MakersAsylumIndia/IS2026_SU_Team02_NeuroPixel/Photos_Videos/Images/PHOTO-2026-05-30-21-31-18.jpg

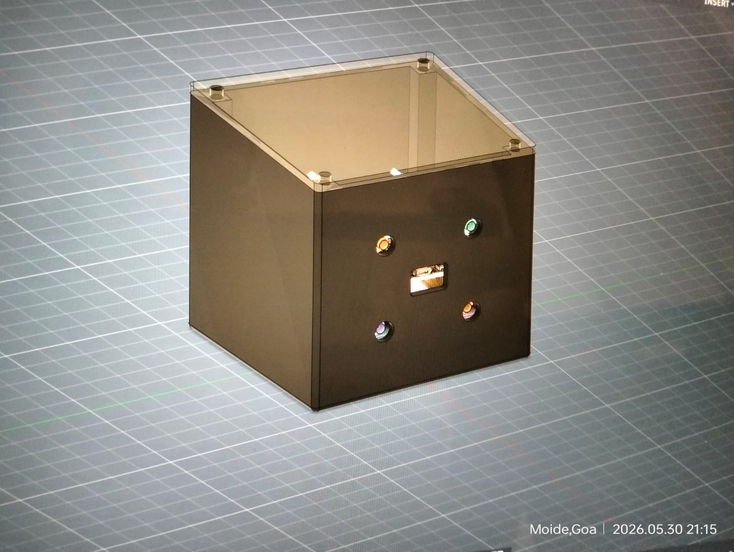
Photos_Videos/Images/PHOTO-2026-05-30-21-31-18.jpg
