MakersAsylumIndia/IS2026_SU_Team02_NeuroPixel/Reference_Data/EMG-Pinout.jpg

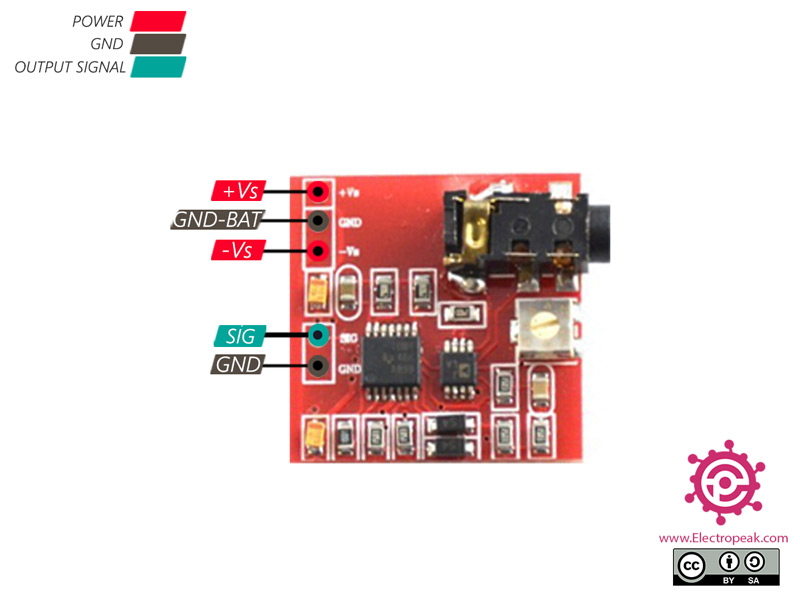
Reference_Data/EMG-Pinout.jpg
