MakersAsylumIndia/IS2026_SU_Team02_NeuroPixel/Photos_Videos/Images/IMG_3430.JPG

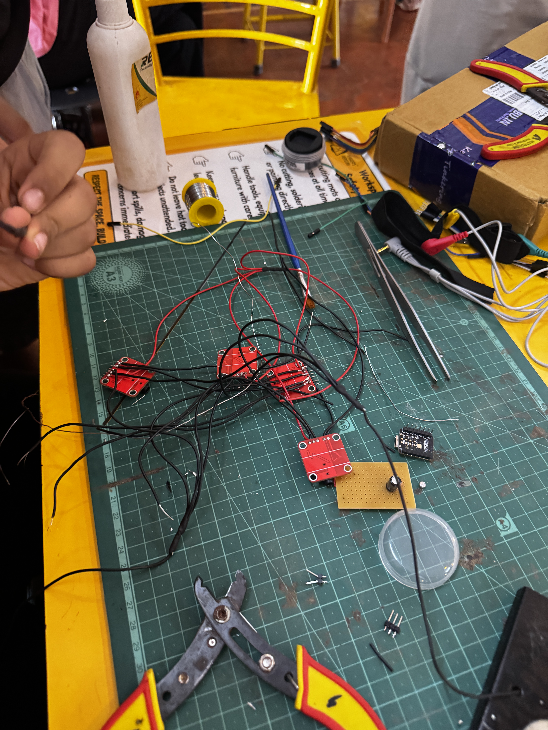
Photos_Videos/Images/IMG_3430.JPG
